dymczykm/HubertTheHumidityLogger/firmware/humidity_logger/influxdb.h

#include "sim7600.h"

#define USER "xxx"
#define PASSWORD "xxx"
#define DB_URL "xxx"

bool postToDatabase(String feed, const String& key, const float& temperature, const float& humidity, const float& pressure);
